MOSH-Insa-Toulouse/2024-2025-4GP-Racheleifrg-Krndnd/Androïd_app/Flex&graph/my_app_inventor/code_part1.PNG

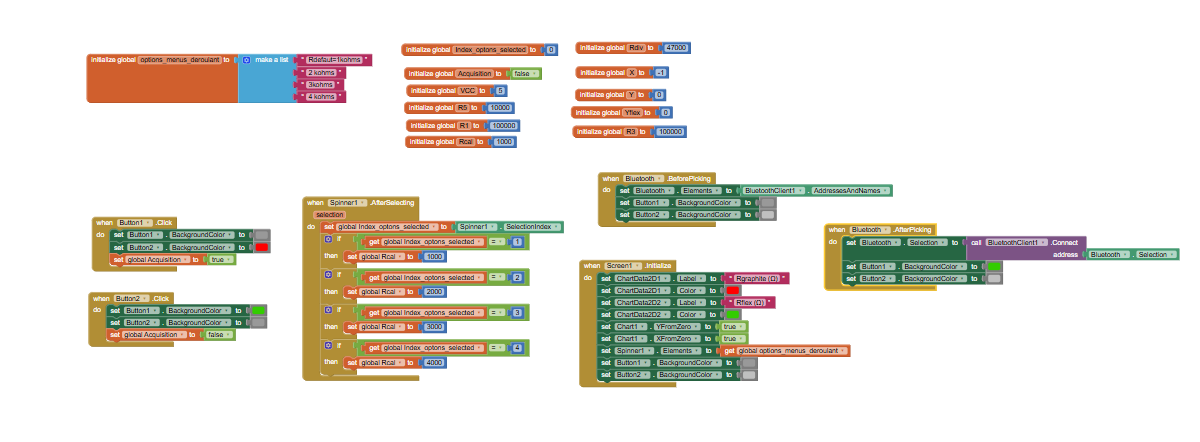
Androïd_app/Flex&graph/my_app_inventor/code_part1.PNG
