MOSH-Insa-Toulouse/2024-2025-4GP-Racheleifrg-Krndnd/Androïd_app/Flex&graph/my_app_inventor/scree_on_my_app_inventor.PNG

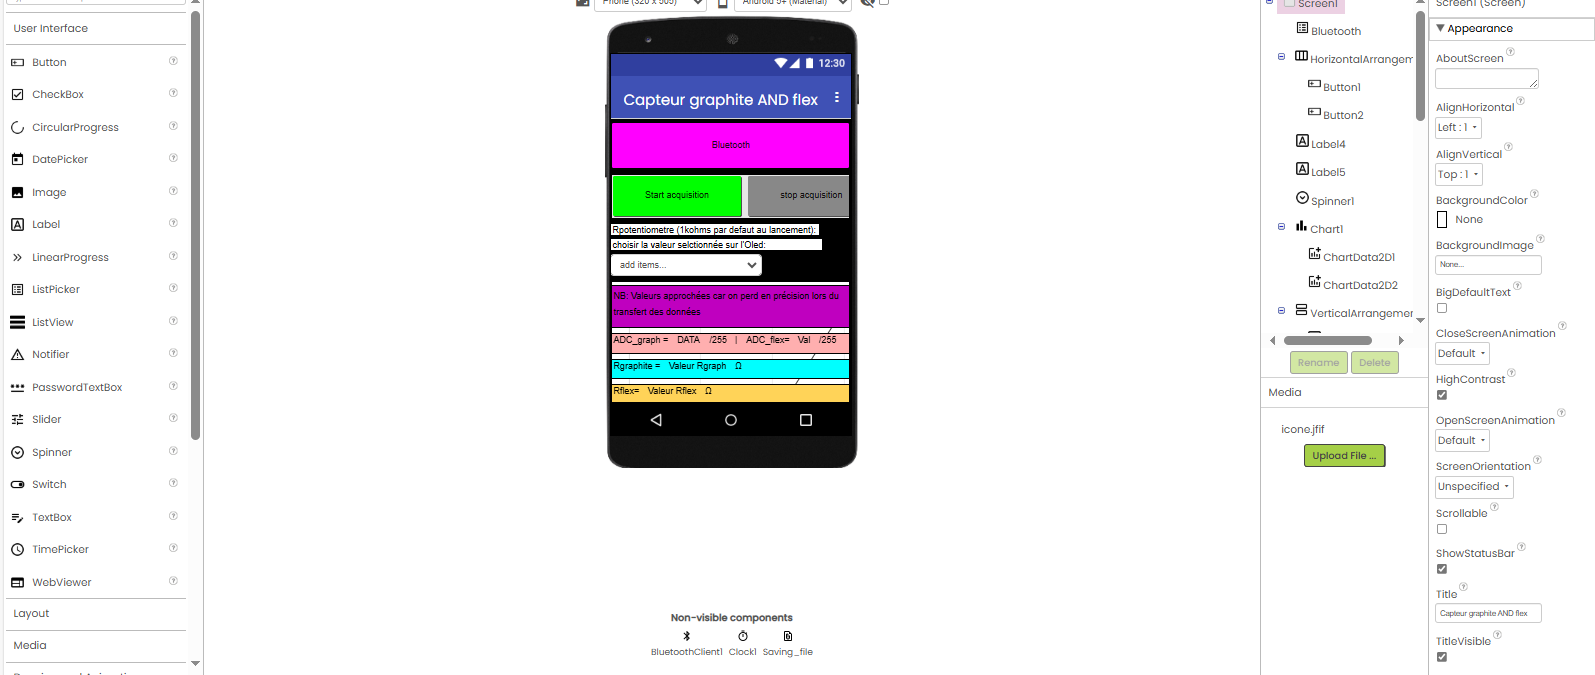
Androïd_app/Flex&graph/my_app_inventor/scree_on_my_app_inventor.PNG
