MOSH-Insa-Toulouse/2024-2025-4GP-Racheleifrg-Krndnd/Androïd_app/Flex_OR_graph/My_app_inventor/code_part_1.PNG

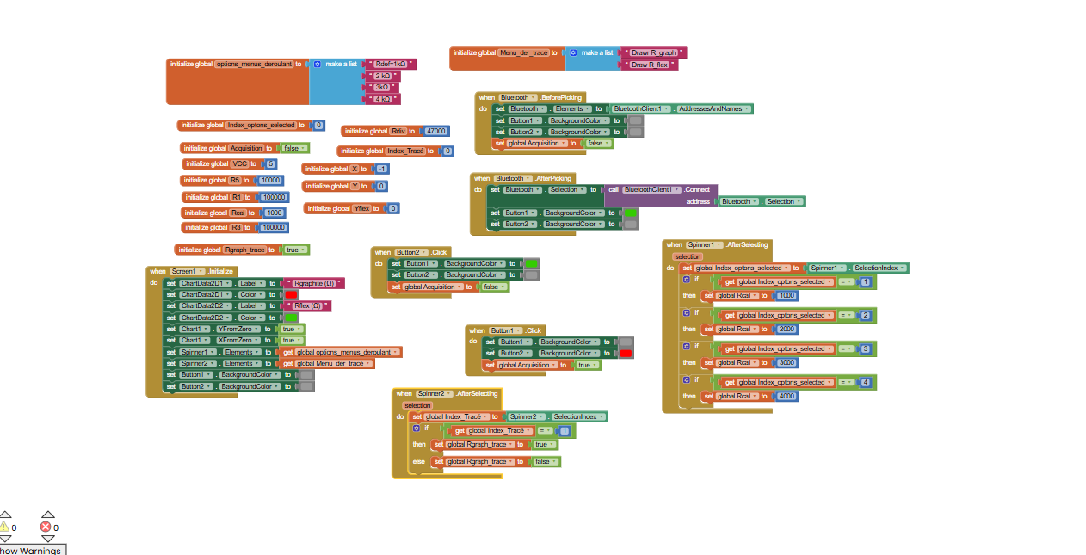
Androïd_app/Flex_OR_graph/My_app_inventor/code_part_1.PNG
