MOSH-Insa-Toulouse/2024-2025-4GP-Racheleifrg-Krndnd/KiCad/PCB_KiCad_models/3D_PCB_view1.jpg

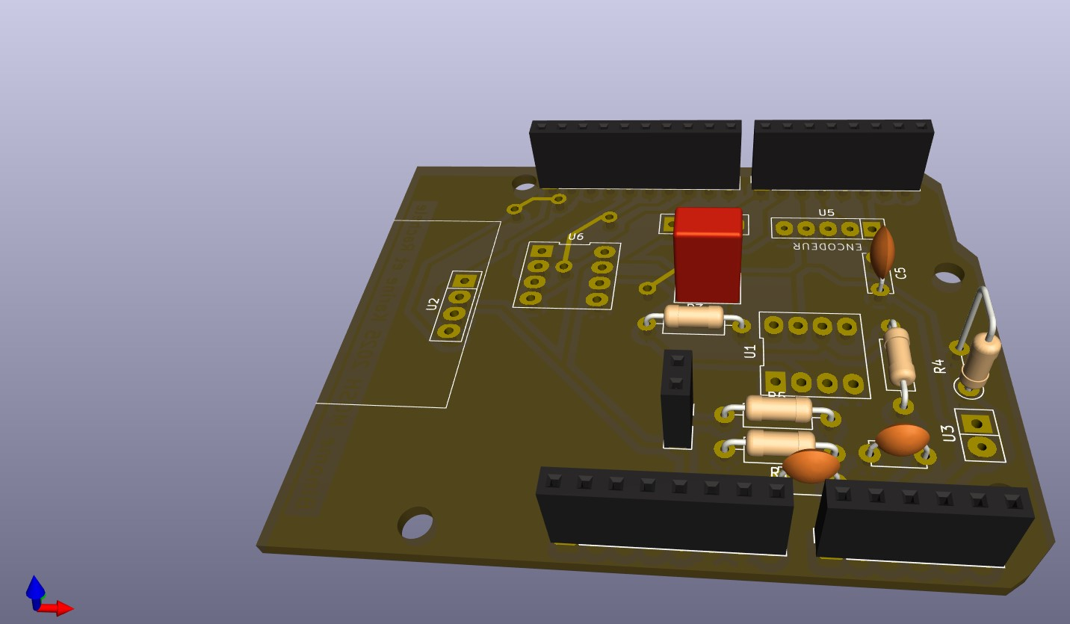
KiCad/PCB_KiCad_models/3D_PCB_view1.jpg
