MOSH-Insa-Toulouse/2024-2025-4GP-Racheleifrg-Krndnd/KiCad/PCB_KiCad_models/KiCad_schematic.jpg

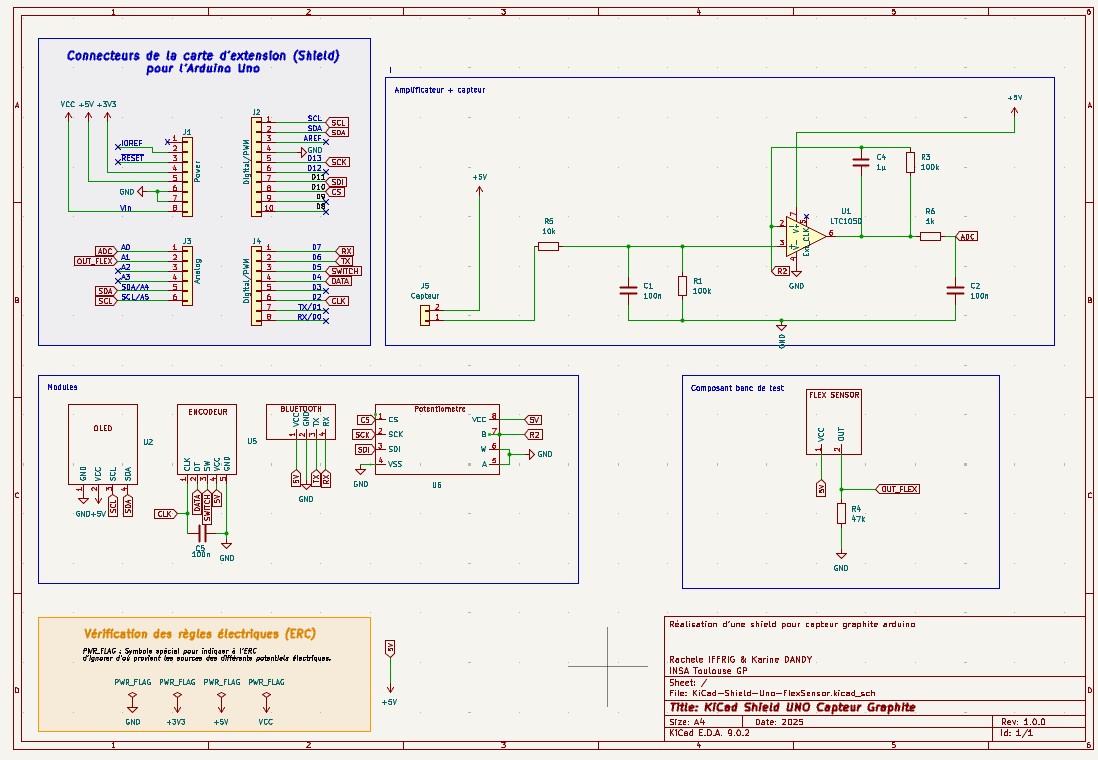
KiCad/PCB_KiCad_models/KiCad_schematic.jpg
