MOSH-Insa-Toulouse/2024-2025-4GP-Racheleifrg-Krndnd/KiCad/PCB_KiCad_models/PCB.jpg

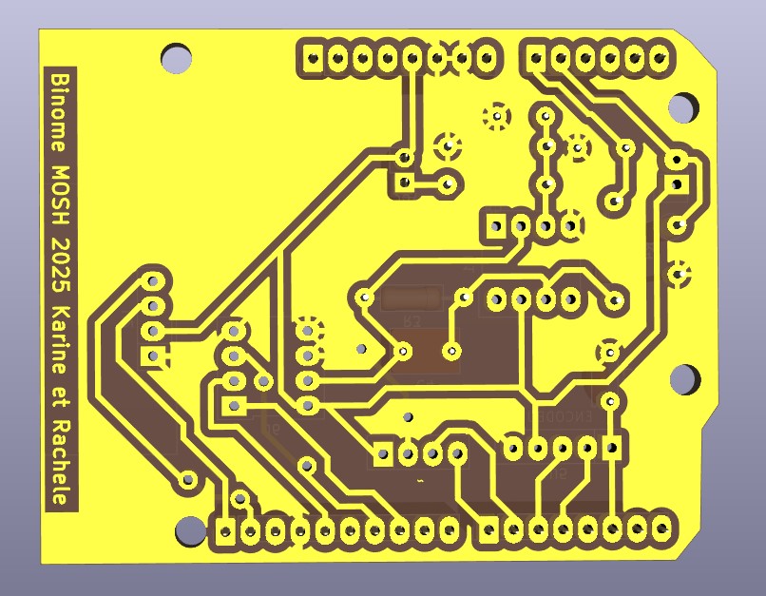
KiCad/PCB_KiCad_models/PCB.jpg
