MOSH-Insa-Toulouse/2024-2025-4GP-Racheleifrg-Krndnd/Androïd_app/Flex&graph/on_the_phone/step4.jpg

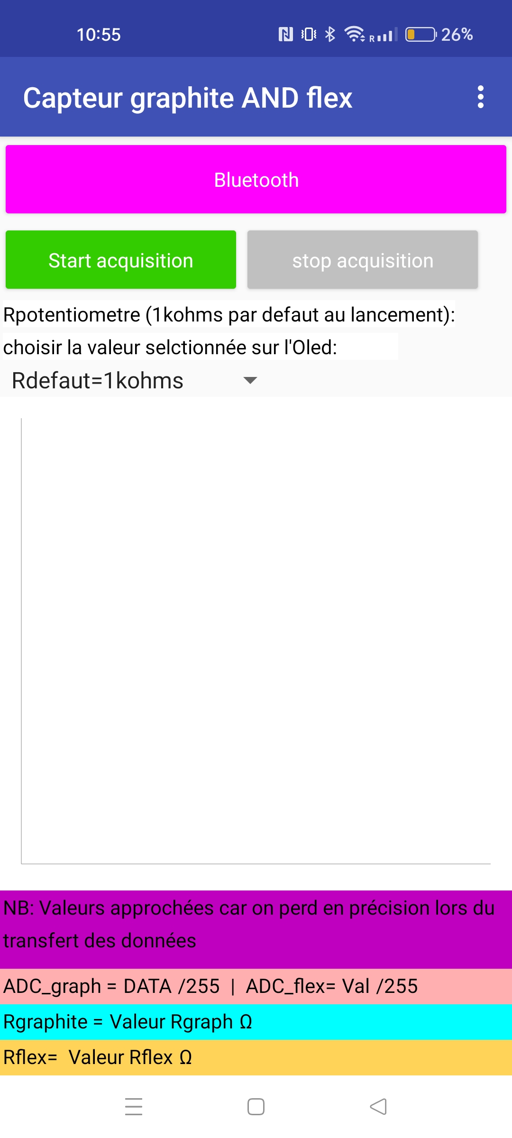
Androïd_app/Flex&graph/on_the_phone/step4.jpg
