MOSH-Insa-Toulouse/2024-2025-4GP-Racheleifrg-Krndnd/Androïd_app/Flex_OR_graph/on_the_phone/step7_flex.jpg

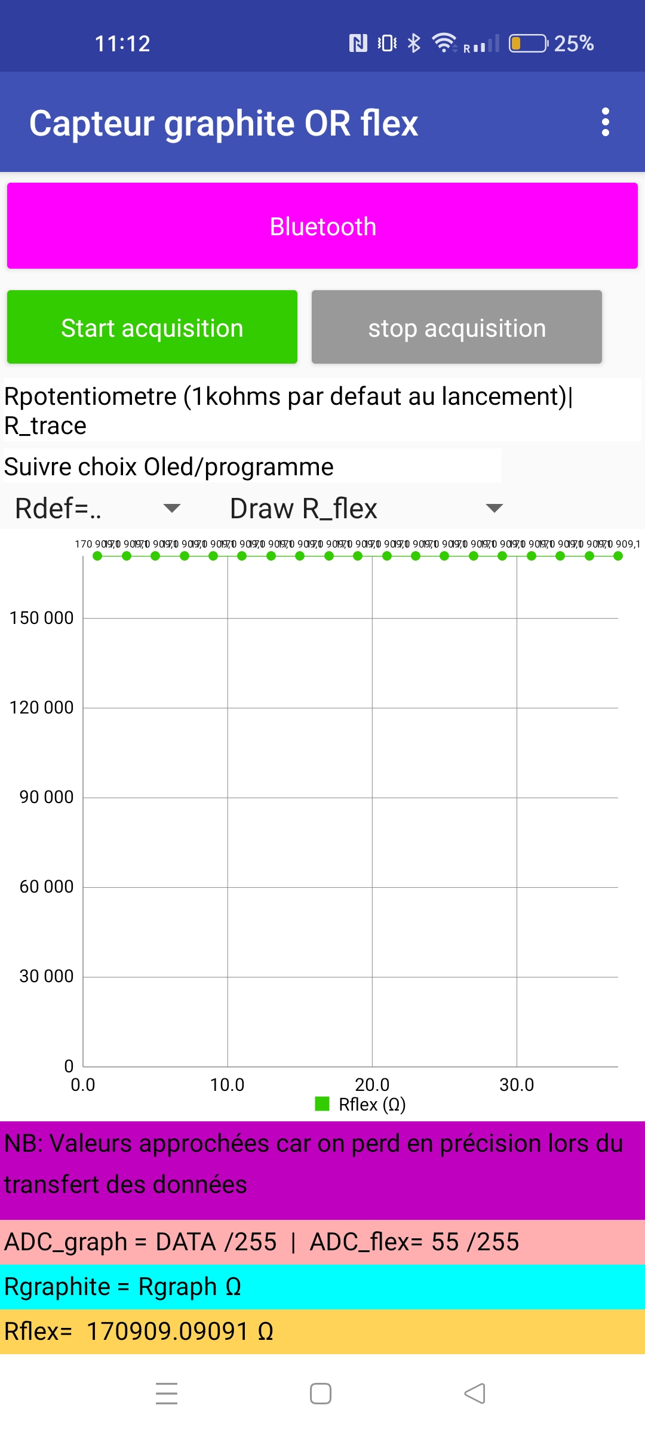
Androïd_app/Flex_OR_graph/on_the_phone/step7_flex.jpg
