MOSH-Insa-Toulouse/2024-2025-4GP-Racheleifrg-Krndnd/Bench_test/graphite_based_sensor.jpg

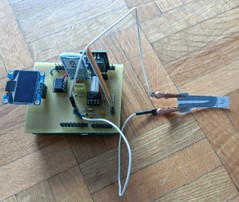
Bench_test/graphite_based_sensor.jpg
