MOSH-Insa-Toulouse/2024-2025-4GP-Racheleifrg-Krndnd/Datasheet/Flex_sensor__results_in_tension.png

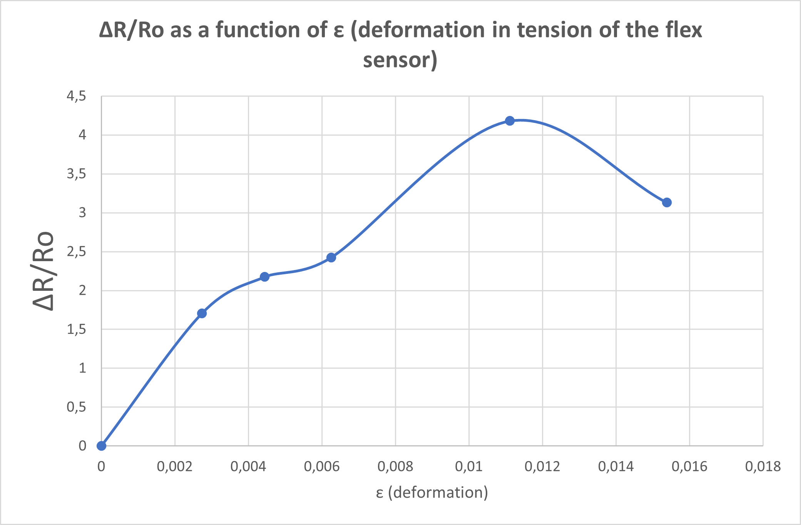
Datasheet/Flex_sensor__results_in_tension.png
