MOSH-Insa-Toulouse/2024-2025-4GP-Racheleifrg-Krndnd/Datasheet/Graphite_sensor__results_in_compression.png

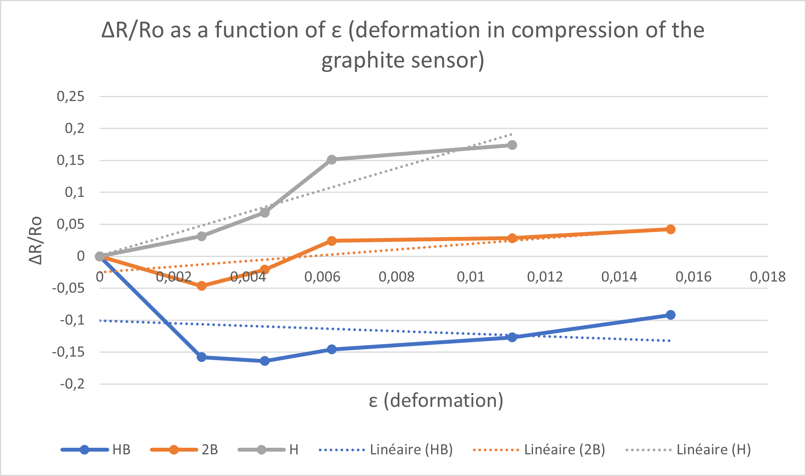
Datasheet/Graphite_sensor__results_in_compression.png
