MOSH-Insa-Toulouse/2024-2025-4GP-Racheleifrg-Krndnd/Datasheet/Graphite_sensor__results_in_tension.png

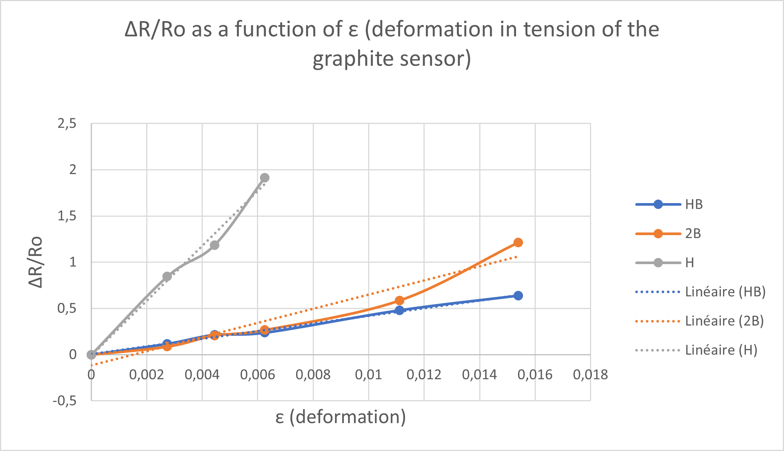
Datasheet/Graphite_sensor__results_in_tension.png
